rolohaun/Rook-180/STL/Toolhead/Toolhead_TD6S.stl

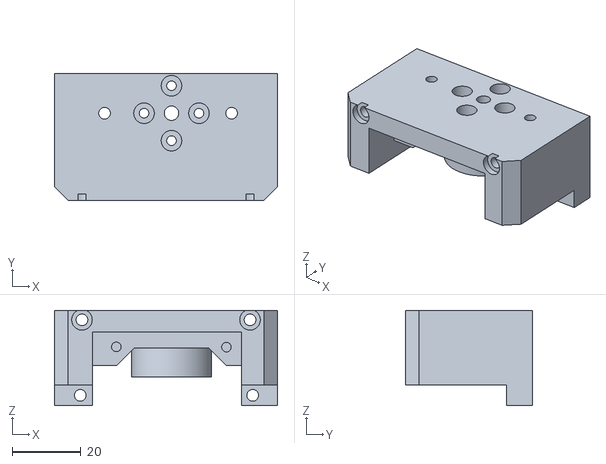
[picture p16: CAD file, 2023-01-08]
STL/Toolhead/Toolhead_TD6S.stl
65.0 x 37.1 x 27.7
