rolohaun/Rook-180/STL/Frame/Bottom Frame/1 x Rear_Lower_Brace_With_Motor_Mount.stl

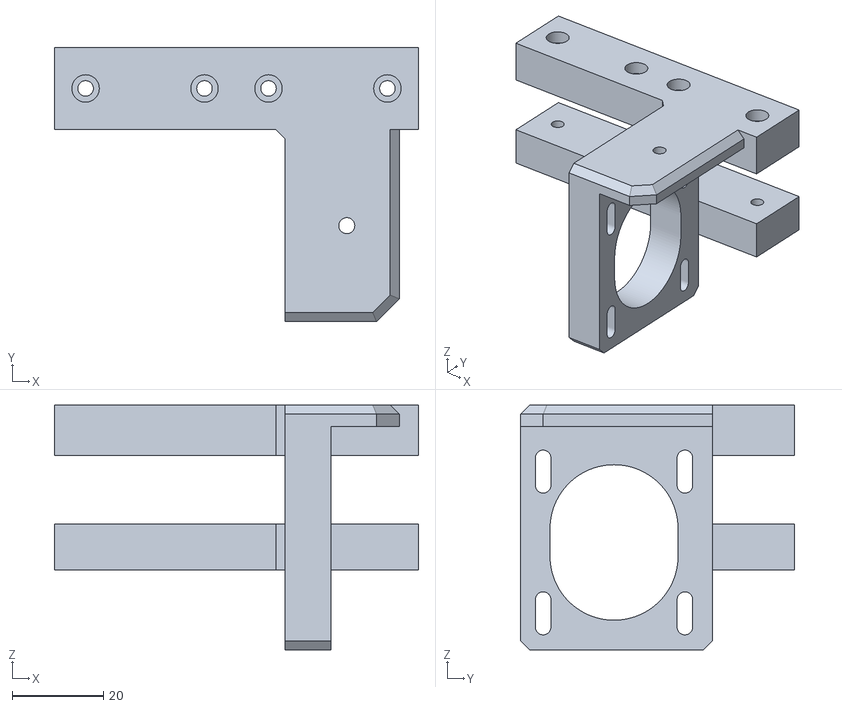
[picture p17: CAD file, 2023-01-08]
STL/Frame/Bottom Frame/1 x Rear_Lower_Brace_With_Motor_Mount.stl
79.6 x 60.0 x 53.6
