rolohaun/Rook-180/STL/Frame/Top Frame/Rear_Right_Y_Frame_Clamp.stl

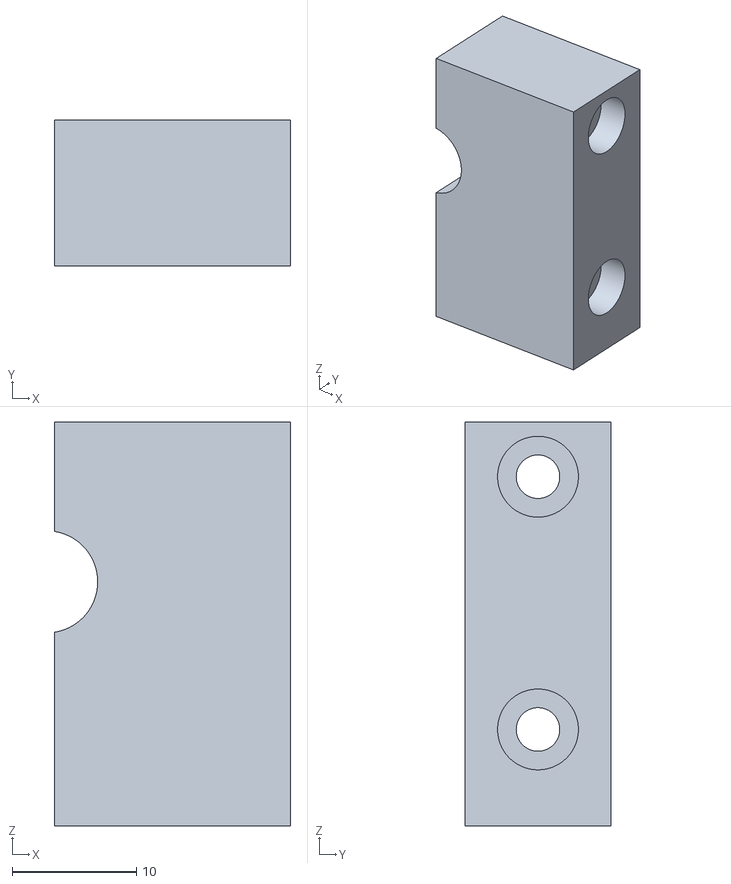
[picture p18: CAD file, 2023-01-10]
STL/Frame/Top Frame/Rear_Right_Y_Frame_Clamp.stl
19.0 x 11.7 x 32.5
