rolohaun/Rook-180/STL/Bed/Rear_Bed_mount.stl

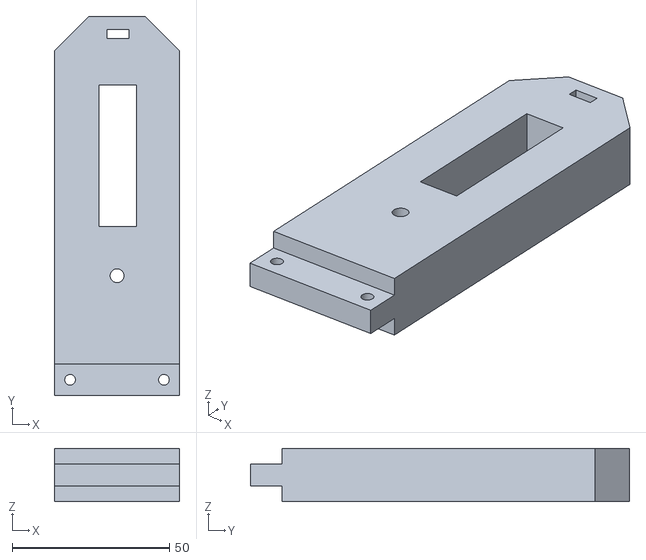
[picture p19: CAD file, 2023-01-22]
STL/Bed/Rear_Bed_mount.stl
39.9 x 120.6 x 17.0
