rolohaun/Rook-180/STL/Frame/Bottom Frame/3 x Frame_Lower_Brace.stl

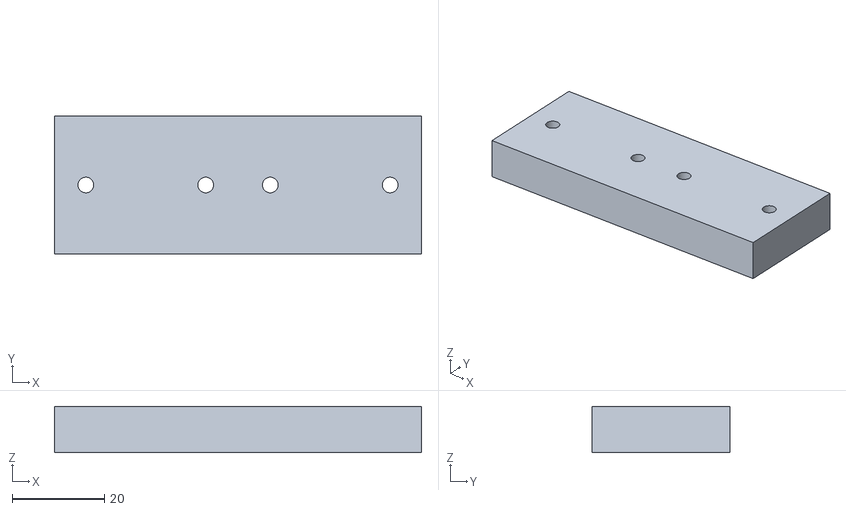
[picture p20: CAD file, 2023-01-08]
STL/Frame/Bottom Frame/3 x Frame_Lower_Brace.stl
79.6 x 30.0 x 10.0
