rolohaun/Rook-180/STL/Bed/Left_Bed_Bearing_Clamp.stl

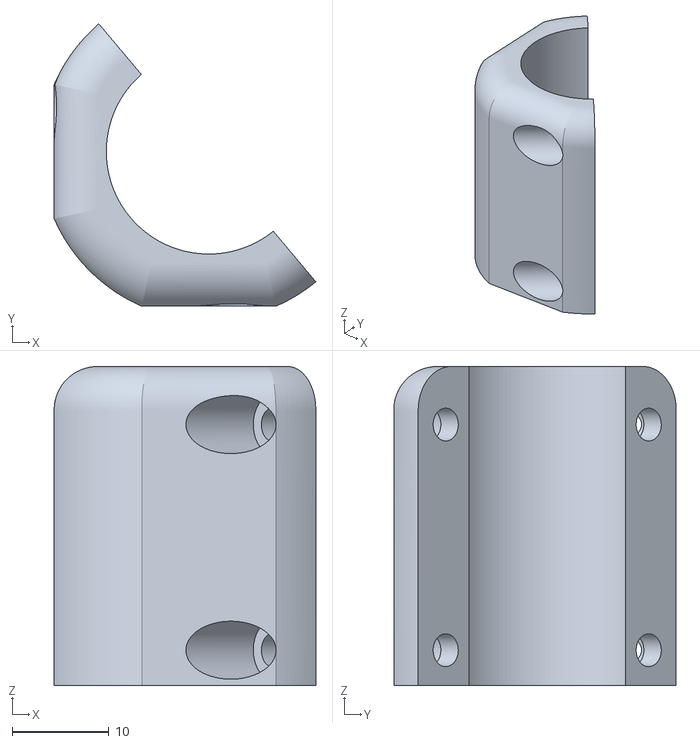
[picture p21: CAD file, 2023-01-08]
STL/Bed/Left_Bed_Bearing_Clamp.stl
27.1 x 29.2 x 33.0
