rolohaun/Rook-180/STL/Frame/Top Frame/Front_Left_Y_Frame_Clamp.stl

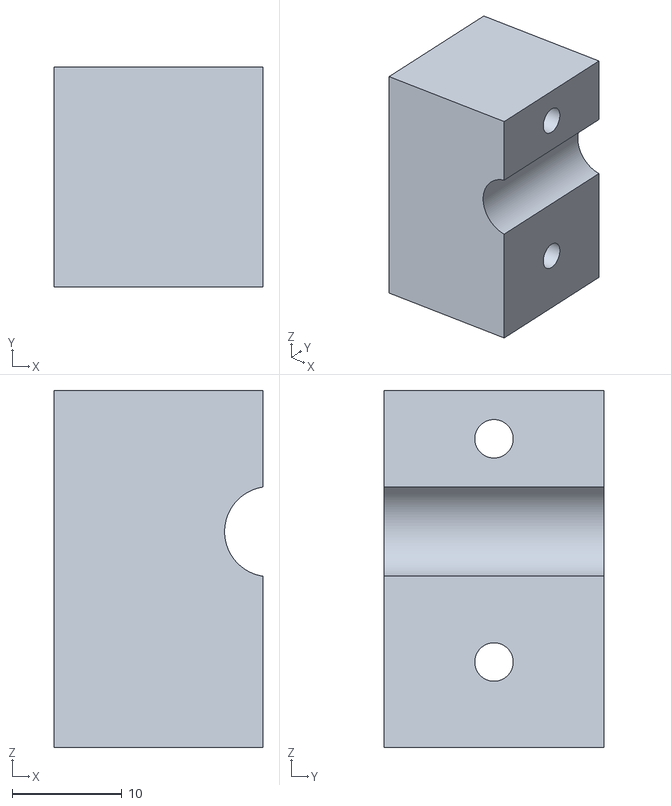
[picture p22: CAD file, 2023-01-08]
STL/Frame/Top Frame/Front_Left_Y_Frame_Clamp.stl
19.0 x 20.0 x 32.5
