rolohaun/Rook-180/STL/Frame/Top Frame/1 x Rear_Upper_Brace.stl

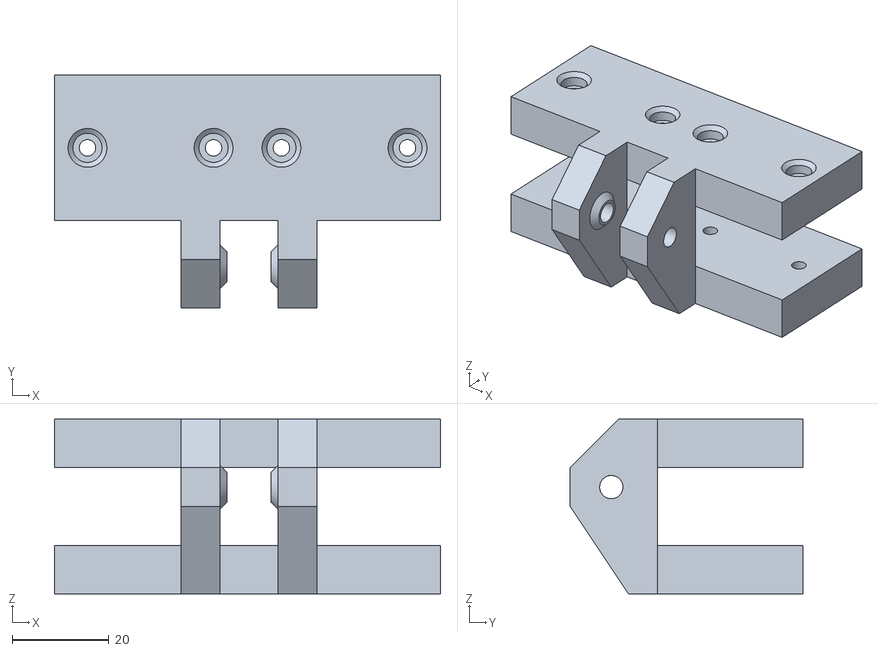
[picture p23: CAD file, 2023-01-08]
STL/Frame/Top Frame/1 x Rear_Upper_Brace.stl
79.6 x 48.0 x 36.0
