rolohaun/Rook-180/STL/Frame/Top Frame/TOP_Right_Front_Frame.stl

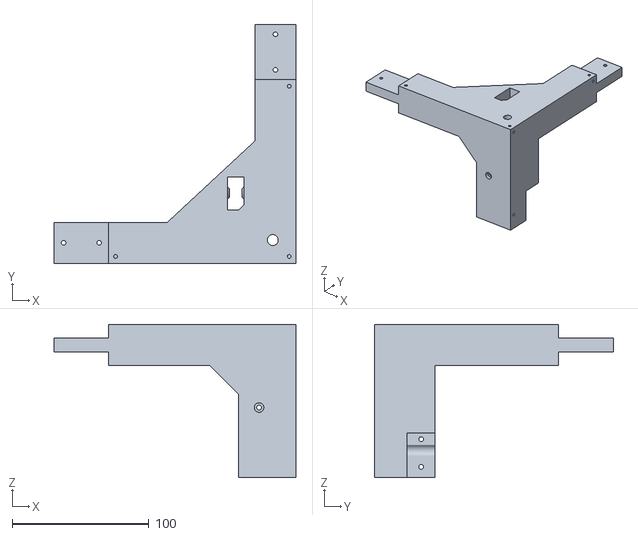
[picture p24: CAD file, 2023-01-08]
STL/Frame/Top Frame/TOP_Right_Front_Frame.stl
177.0 x 174.5 x 112.0
